EjaadTech/Engineers-Multi-Tool/hardware/IMG_5694.JPG

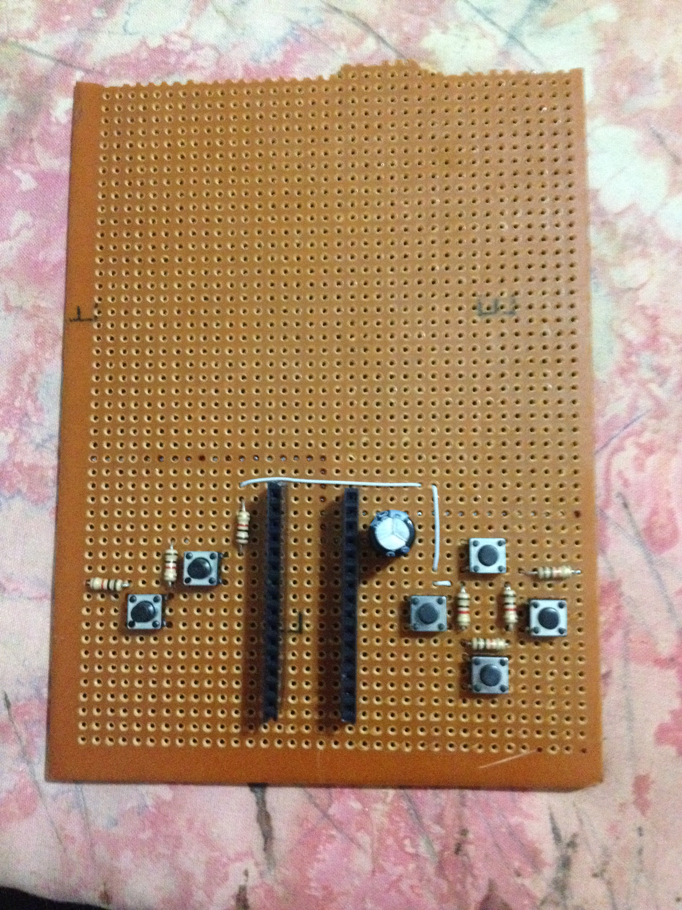
hardware/IMG_5694.JPG
