EjaadTech/Engineers-Multi-Tool/hardware/IMG_5698.JPG

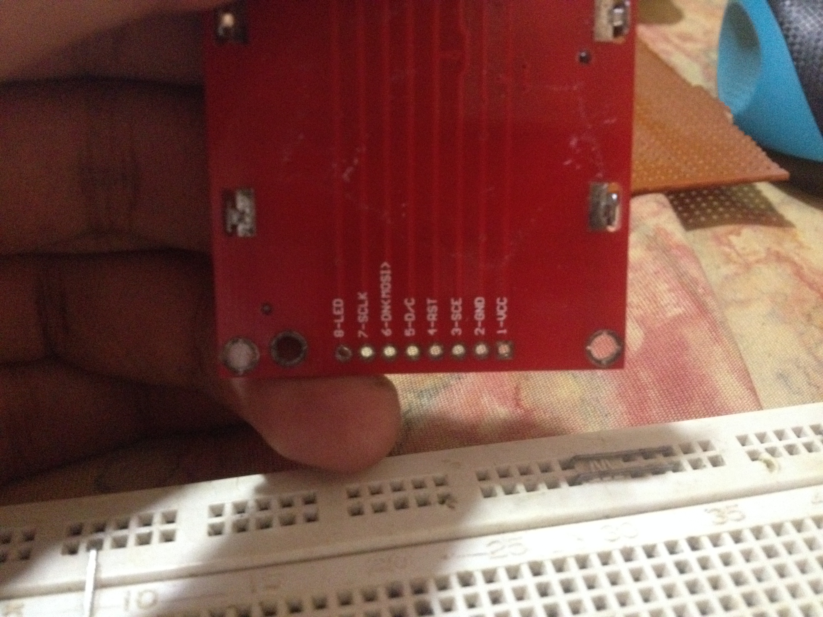
hardware/IMG_5698.JPG
