EjaadTech/Engineers-Multi-Tool/hardware/IMG_5699.JPG

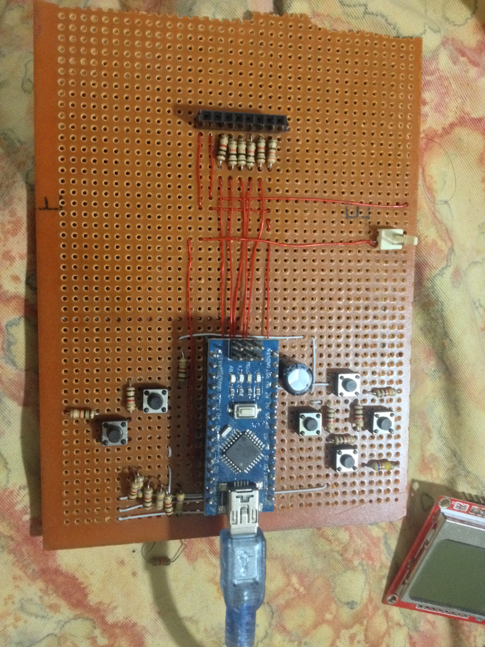
hardware/IMG_5699.JPG
