EjaadTech/Engineers-Multi-Tool/hardware/IMG_5701.JPG

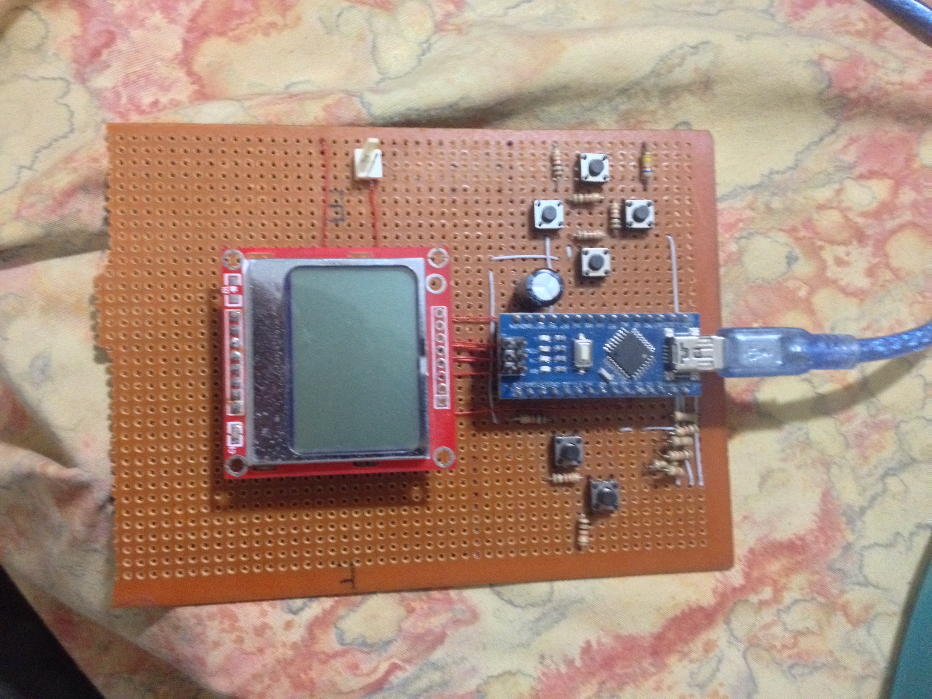
hardware/IMG_5701.JPG
