EjaadTech/Engineers-Multi-Tool/hardware/IMG_5702.JPG

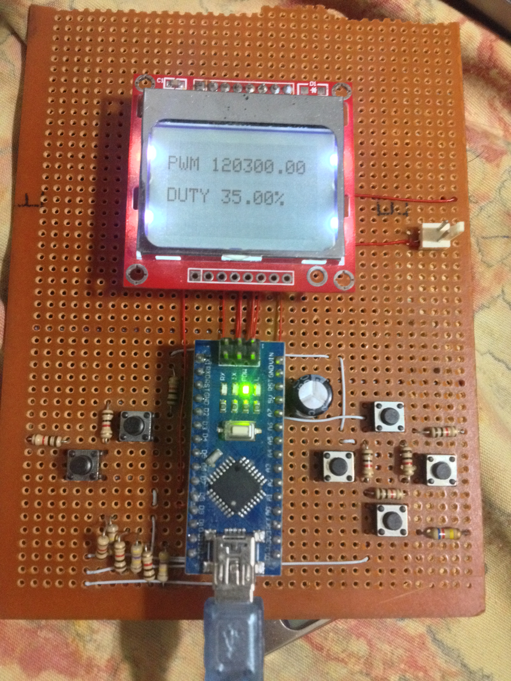
hardware/IMG_5702.JPG
