EjaadTech/Engineers-Multi-Tool/hardware/IMG_5704.JPG

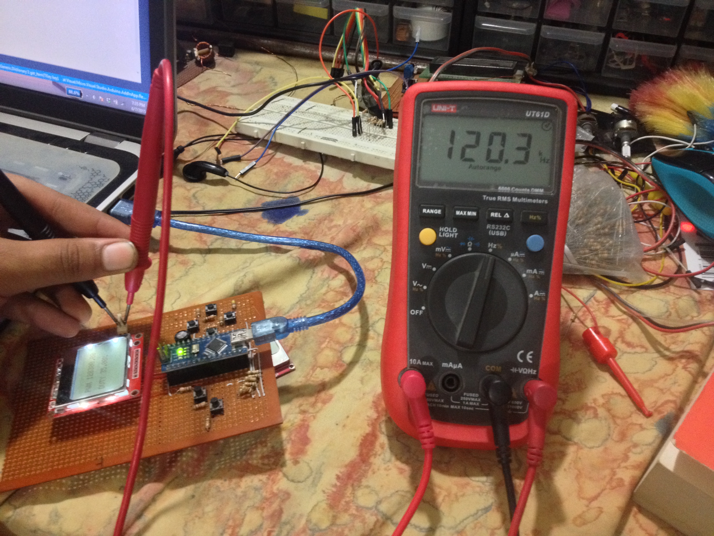
hardware/IMG_5704.JPG
