EjaadTech/Engineers-Multi-Tool/hardware/IMG_5705.JPG

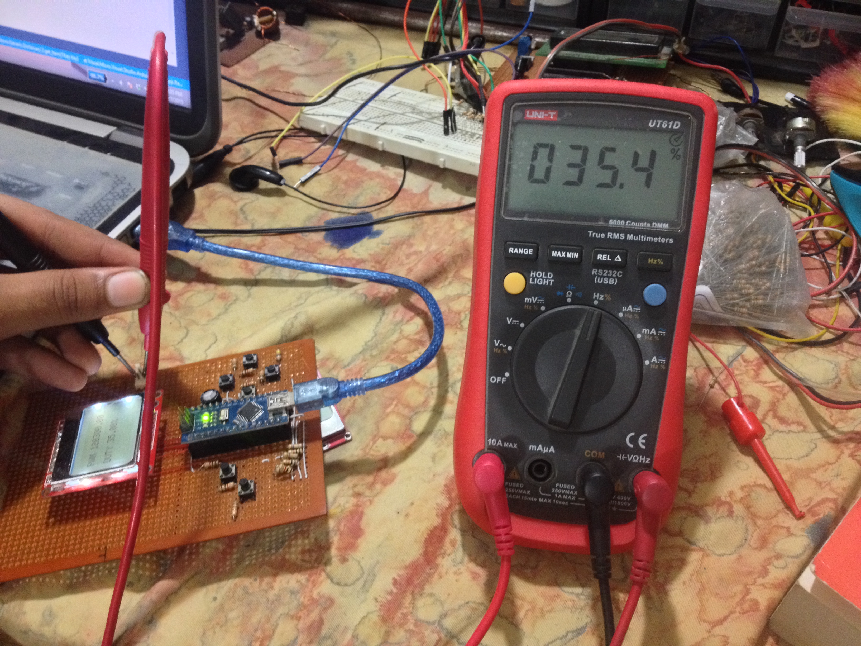
hardware/IMG_5705.JPG
