EjaadTech/Engineers-Multi-Tool/hardware/IMG_20150610_111421_223.jpg

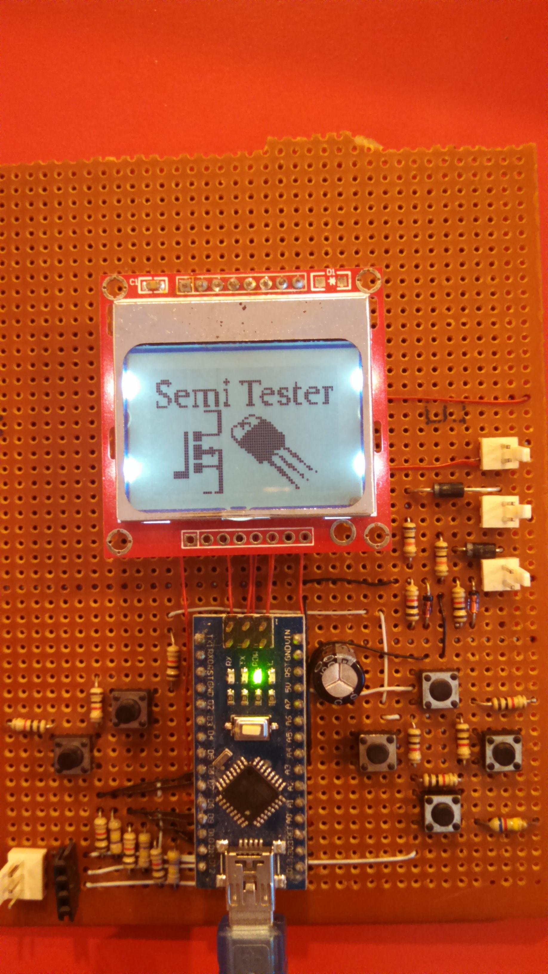
hardware/IMG_20150610_111421_223.jpg
