EjaadTech/Engineers-Multi-Tool/hardware/IMG_20150610_111428_892.jpg

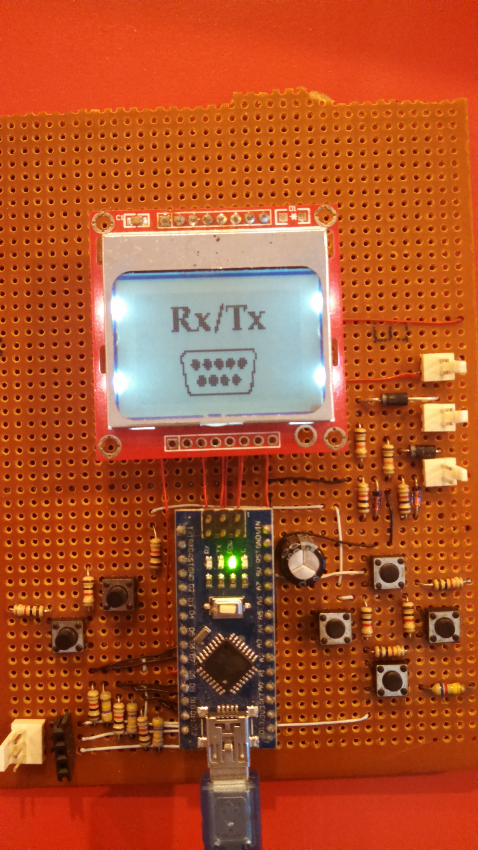
hardware/IMG_20150610_111428_892.jpg
