EjaadTech/Engineers-Multi-Tool/hardware/IMG_20150610_111452_189.jpg

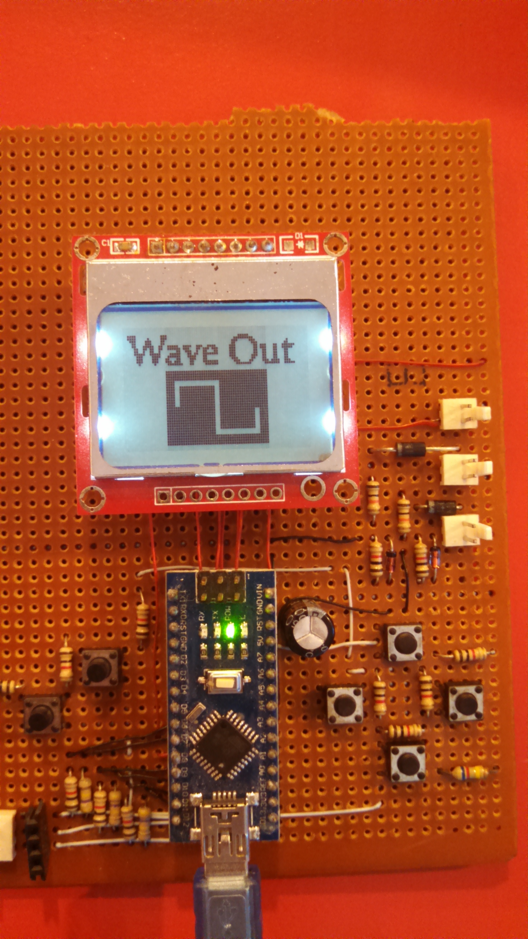
hardware/IMG_20150610_111452_189.jpg
