EjaadTech/Engineers-Multi-Tool/firmware/emt/menu.h

#include <avr/pgmspace.h>

const unsigned char PROGMEM voltmeter[] = {
	0x0, 0x0, 0x0, 0x0, 0x0, 0x0, 0x0, 0x0, 0x0, 0x0, 0x0,
	0x0, 0x0, 0x0, 0x0, 0x0, 0x0, 0x0, 0x0, 0x0, 0x0, 0x0,
	0x0, 0x0, 0x0, 0x0, 0x0, 0x0, 0x0, 0x0, 0x0, 0x0, 0x0,
	0x0, 0x0, 0x1, 0xc0, 0x0, 0x0, 0x0, 0x0, 0x0, 0x0, 0x0,
	0x1c, 0x1c, 0x0, 0xc0, 0x1, 0xc0, 0x70, 0x0, 0x0, 0x0, 0x0,
	0x1c, 0x18, 0x0, 0xc0, 0x1, 0xc0, 0xe0, 0x0, 0x0, 0x0, 0x0,
	0xc, 0x10, 0x0, 0xc4, 0x1, 0xe0, 0xe0, 0x1, 0x80, 0x0, 0x0,
	0xc, 0x31, 0xe0, 0xcf, 0x81, 0x61, 0xe0, 0xe3, 0xe3, 0xc6, 0xc0,
	0x6, 0x23, 0x38, 0xcf, 0x1, 0x31, 0x63, 0x33, 0xe6, 0x67, 0xc0,
	0x6, 0x66, 0x18, 0xcc, 0x1, 0xb3, 0x63, 0x19, 0x8c, 0x62, 0x40,
	0x3, 0x46, 0xc, 0xcc, 0x1, 0xba, 0x63, 0xf9, 0x8f, 0xe2, 0x0,
	0x3, 0x46, 0xc, 0xcc, 0x1, 0x9e, 0x63, 0x1, 0x8c, 0x6, 0x0,
	0x3, 0x86, 0x18, 0xcc, 0x1, 0x9c, 0x63, 0x1, 0x8c, 0x2, 0x0,
	0x1, 0x83, 0x18, 0xce, 0x1, 0x8c, 0x63, 0x81, 0x87, 0x6, 0x0,
	0x1, 0x81, 0xf1, 0xc7, 0x83, 0x88, 0x70, 0xf1, 0xe3, 0xe7, 0x0,
	0x0, 0x0, 0x0, 0x0, 0x0, 0x0, 0x0, 0x0, 0x0, 0x0, 0x0,
	0x0, 0x0, 0x0, 0x0, 0x0, 0x0, 0x0, 0x0, 0x0, 0x0, 0x0,
	0x0, 0x0, 0x0, 0x0, 0x0, 0x0, 0x0, 0x0, 0x0, 0x0, 0x0,
	0x0, 0x0, 0x0, 0x0, 0x0, 0x0, 0x0, 0x0, 0x0, 0x0, 0x0,
	0x0, 0x0, 0x0, 0x10, 0x3f, 0xe0, 0xf8, 0x0, 0x0, 0x0, 0x0,
	0x0, 0x0, 0x0, 0x18, 0x3f, 0xff, 0xff, 0x0, 0x0, 0x0, 0x0,
	0x0, 0x0, 0x0, 0x8, 0x30, 0x3e, 0x3, 0xc0, 0x0, 0x0, 0x0,
	0x0, 0x0, 0x0, 0xc, 0x10, 0x8, 0x0, 0xe0, 0x0, 0x0, 0x0,
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
	0x0, 0x0, 0x0, 0x81, 0xc7, 0x18, 0x60, 0x20, 0x0, 0x0, 0x0,
	0x0, 0x0, 0x0, 0x81, 0xef, 0xbc, 0xf0, 0x20, 0x0, 0x0, 0x0,
	0x0, 0x0, 0x0, 0x83, 0xef, 0xbe, 0xf8, 0x20, 0x0, 0x0, 0x0,
	0x0, 0x0, 0x0, 0x83, 0xef, 0xbc, 0xf0, 0x20, 0x0, 0x0, 0x0,
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
};
